lambdamikel/LambdaSpeak/images/ls195-pcb1.jpg

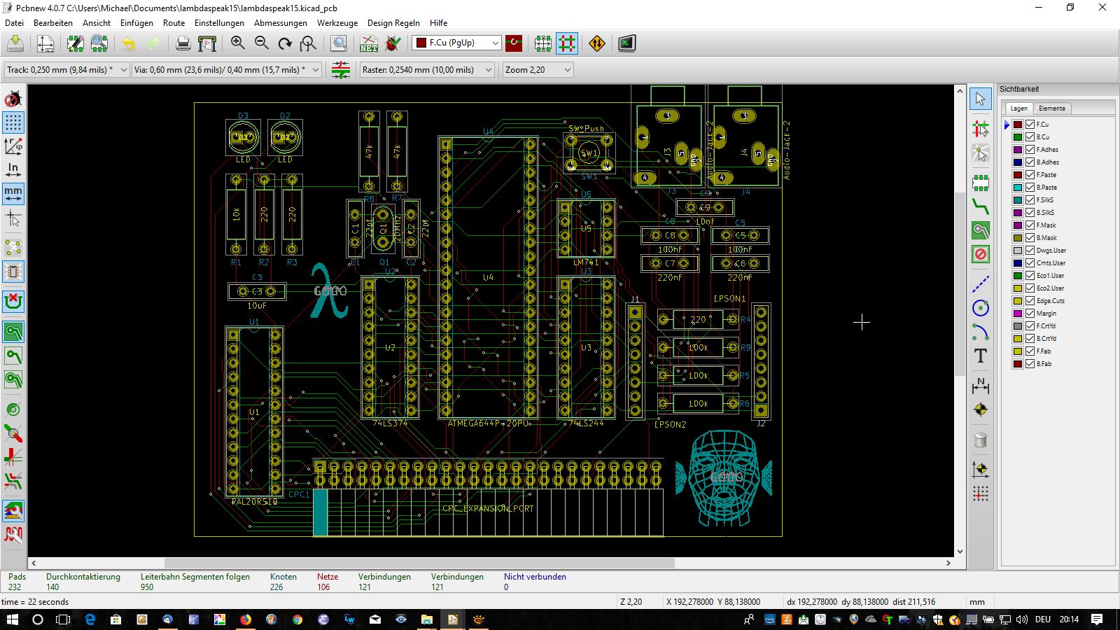
images/ls195-pcb1.jpg
