lambdamikel/LambdaSpeak/images/ls195-pcb2.jpg

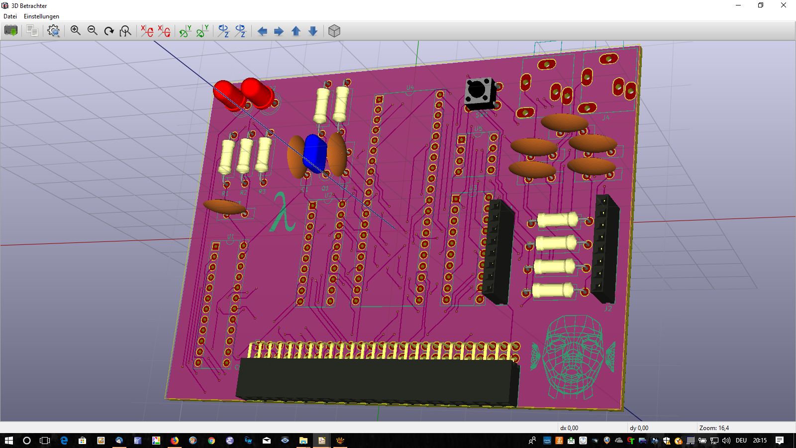
images/ls195-pcb2.jpg
