lambdamikel/LambdaSpeak/images/ls199-pcb1.jpg

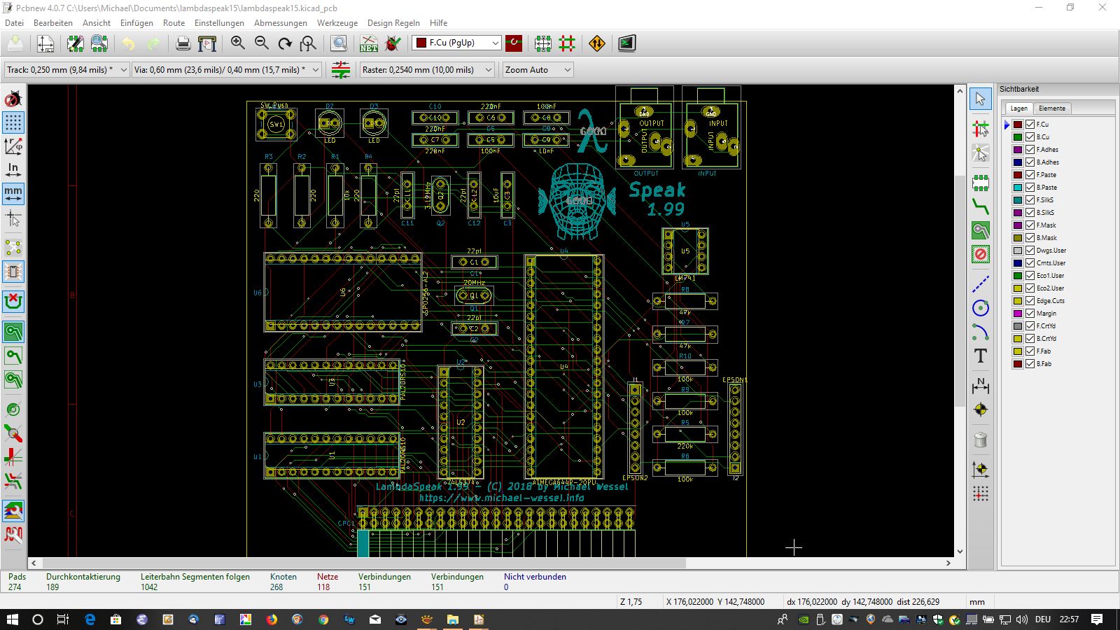
images/ls199-pcb1.jpg
