lambdamikel/LambdaSpeak/images/ls199-pcb2.jpg

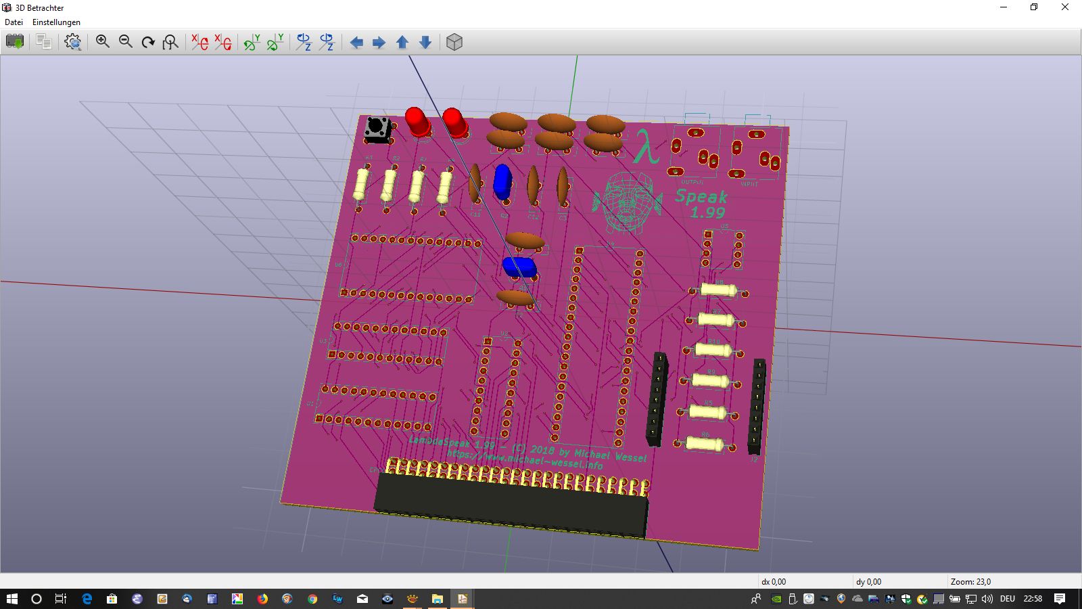
images/ls199-pcb2.jpg
